scottlbaker/ADX-MINI/firmware/MI3/si5351.h

// ============================================================================
//
// si5351.h - Si5351 library for Arduino
//
// Copyright (C) 2015 - 2019 Jason Milldrum <milldrum@gmail.com>
//                           Dana H. Myers <k6jq@comcast.net>
//
// Some tuning algorithms derived from clk-si5351.c in the Linux kernel.
// Sebastian Hesselbarth <sebastian.hesselbarth@gmail.com>
// Rabeeh Khoury <rabeeh@solid-run.com>
//
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
// ============================================================================

#ifndef SI5351_H_
#define SI5351_H_

#define SI5351_I2C_ADDR                 0x60
#define SI5351_XTAL_FREQ                25000000
#define SI5351_PLL_FIXED                80000000000ULL
#define SI5351_FREQ_MULT                100ULL
#define SI5351_DEFAULT_CLK              1000000000ULL

#define SI5351_PLL_VCO_MIN              600000000
#define SI5351_PLL_VCO_MAX              900000000
#define SI5351_MULTISYNTH_MIN_FREQ      500000
#define SI5351_MULTISYNTH_DIVBY4_FREQ   150000000
#define SI5351_MULTISYNTH_MAX_FREQ      225000000
#define SI5351_MULTISYNTH_SHARE_MAX     100000000
#define SI5351_MULTISYNTH_SHARE_MIN     1024000
#define SI5351_CLKOUT_MIN_FREQ          4000
#define SI5351_CLKOUT_MAX_FREQ          SI5351_MULTISYNTH_MAX_FREQ

#define SI5351_PLL_A_MIN                15
#define SI5351_PLL_A_MAX                90
#define SI5351_PLL_B_MAX                (SI5351_PLL_C_MAX-1)
#define SI5351_PLL_C_MAX                1048575
#define SI5351_MULTISYNTH_A_MIN         6
#define SI5351_MULTISYNTH_A_MAX         1800
#define SI5351_MULTISYNTH_B_MAX         (SI5351_MULTISYNTH_C_MAX-1)
#define SI5351_MULTISYNTH_C_MAX         1048575
#define SI5351_MULTISYNTH_P1_MAX        ((1<<18)-1)
#define SI5351_MULTISYNTH_P2_MAX        ((1<<20)-1)
#define SI5351_MULTISYNTH_P3_MAX        ((1<<20)-1)
#define SI5351_VCXO_PULL_MIN            30
#define SI5351_VCXO_PULL_MAX            240
#define SI5351_VCXO_MARGIN              103

#define SI5351_DEVICE_STATUS            0
#define SI5351_INTERRUPT_STATUS         1
#define SI5351_INTERRUPT_MASK           2
#define SI5351_STATUS_SYS_INIT          (1<<7)
#define SI5351_STATUS_LOL_B             (1<<6)
#define SI5351_STATUS_LOL_A             (1<<5)
#define SI5351_STATUS_LOS               (1<<4)
#define SI5351_OUTPUT_ENABLE_CTRL       3
#define SI5351_OEB_PIN_ENABLE_CTRL      9
#define SI5351_PLL_INPUT_SOURCE         15
#define SI5351_PLL_INPUT_XO             0
#define SI5351_PLL_INPUT_CLKIN          1

#define SI5351_CLKIN_DIV_MASK           (3<<6)
#define SI5351_CLKIN_DIV_1              (0<<6)
#define SI5351_CLKIN_DIV_2              (1<<6)
#define SI5351_CLKIN_DIV_4              (2<<6)
#define SI5351_CLKIN_DIV_8              (3<<6)
#define SI5351_PLLB_SOURCE              (1<<3)
#define SI5351_PLLA_SOURCE              (1<<2)

#define SI5351_CLK0_CTRL                16
#define SI5351_CLK1_CTRL                17
#define SI5351_CLK2_CTRL                18
#define SI5351_CLK3_CTRL                19
#define SI5351_CLK4_CTRL                20
#define SI5351_CLK5_CTRL                21
#define SI5351_CLK6_CTRL                22
#define SI5351_CLK7_CTRL                23
#define SI5351_CLK_POWERDOWN            (1<<7)
#define SI5351_CLK_INTEGER_MODE         (1<<6)
#define SI5351_CLK_PLL_SELECT           (1<<5)
#define SI5351_CLK_INVERT               (1<<4)
#define SI5351_CLK_INPUT_MASK           (3<<2)
#define SI5351_CLK_INPUT_XTAL           (0<<2)
#define SI5351_CLK_INPUT_CLKIN          (1<<2)
#define SI5351_CLK_INPUT_MULTISYNTH_0_4 (2<<2)
#define SI5351_CLK_INPUT_MULTISYNTH_N   (3<<2)
#define SI5351_CLK_DRIVE_STRENGTH_MASK  (3<<0)
#define SI5351_CLK_DRIVE_STRENGTH_2MA   (0<<0)
#define SI5351_CLK_DRIVE_STRENGTH_4MA   (1<<0)
#define SI5351_CLK_DRIVE_STRENGTH_6MA   (2<<0)
#define SI5351_CLK_DRIVE_STRENGTH_8MA   (3<<0)

#define SI5351_CLK3_0_DISABLE_STATE     24
#define SI5351_CLK7_4_DISABLE_STATE     25
#define SI5351_CLK_DISABLE_STATE_MASK   3
#define SI5351_CLK_DISABLE_STATE_LOW    0
#define SI5351_CLK_DISABLE_STATE_HIGH   1
#define SI5351_CLK_DISABLE_STATE_FLOAT  2
#define SI5351_CLK_DISABLE_STATE_NEVER  3

#define SI5351_PARAMETERS_LENGTH        8
#define SI5351_PLLA_PARAMETERS          26
#define SI5351_PLLB_PARAMETERS          34
#define SI5351_CLK0_PARAMETERS          42
#define SI5351_CLK1_PARAMETERS          50
#define SI5351_CLK2_PARAMETERS          58
#define SI5351_CLK3_PARAMETERS          66
#define SI5351_CLK4_PARAMETERS          74
#define SI5351_CLK5_PARAMETERS          82
#define SI5351_CLK6_PARAMETERS          90
#define SI5351_CLK7_PARAMETERS          91
#define SI5351_CLK6_7_OUTPUT_DIVIDER    92
#define SI5351_OUTPUT_CLK_DIV_MASK      (7 << 4)
#define SI5351_OUTPUT_CLK6_DIV_MASK     (7 << 0)
#define SI5351_OUTPUT_CLK_DIV_SHIFT     4
#define SI5351_OUTPUT_CLK_DIV6_SHIFT    0
#define SI5351_OUTPUT_CLK_DIV_1         0
#define SI5351_OUTPUT_CLK_DIV_2         1
#define SI5351_OUTPUT_CLK_DIV_4         2
#define SI5351_OUTPUT_CLK_DIV_8         3
#define SI5351_OUTPUT_CLK_DIV_16        4
#define SI5351_OUTPUT_CLK_DIV_32        5
#define SI5351_OUTPUT_CLK_DIV_64        6
#define SI5351_OUTPUT_CLK_DIV_128       7
#define SI5351_OUTPUT_CLK_DIVBY4       (3<<2)

#define SI5351_CLK0                     0
#define SI5351_CLK1                     1
#define SI5351_CLK2                     2
#define SI5351_CLK3                     3
#define SI5351_CLK4                     4
#define SI5351_CLK5                     5
#define SI5351_CLK6                     6
#define SI5351_CLK7                     7

#define SI5351_SSC_PARAM0               149
#define SI5351_SSC_PARAM1               150
#define SI5351_SSC_PARAM2               151
#define SI5351_SSC_PARAM3               152
#define SI5351_SSC_PARAM4               153
#define SI5351_SSC_PARAM5               154
#define SI5351_SSC_PARAM6               155
#define SI5351_SSC_PARAM7               156
#define SI5351_SSC_PARAM8               157
#define SI5351_SSC_PARAM9               158
#define SI5351_SSC_PARAM10              159
#define SI5351_SSC_PARAM11              160
#define SI5351_SSC_PARAM12              161

#define SI5351_VXCO_PARAMETERS_LOW      162
#define SI5351_VXCO_PARAMETERS_MID      163
#define SI5351_VXCO_PARAMETERS_HIGH     164

#define SI5351_CLK0_PHASE_OFFSET        165
#define SI5351_CLK1_PHASE_OFFSET        166
#define SI5351_CLK2_PHASE_OFFSET        167
#define SI5351_CLK3_PHASE_OFFSET        168
#define SI5351_CLK4_PHASE_OFFSET        169
#define SI5351_CLK5_PHASE_OFFSET        170

#define SI5351_PLLA                     0
#define SI5351_PLLB                     1
#define SI5351_PLL_RESET                177
#define SI5351_PLL_RESET_B              (1<<7)
#define SI5351_PLL_RESET_A              (1<<5)
#define SI5351_CRYSTAL_LOAD             183
#define SI5351_CRYSTAL_LOAD_MASK        (3<<6)
#define SI5351_CRYSTAL_LOAD_0PF         (0<<6)
#define SI5351_CRYSTAL_LOAD_6PF         (1<<6)
#define SI5351_CRYSTAL_LOAD_8PF         (2<<6)
#define SI5351_CRYSTAL_LOAD_10PF        (3<<6)

#define SI5351_FANOUT_ENABLE            187
#define SI5351_CLKIN_ENABLE             (1<<7)
#define SI5351_XTAL_ENABLE              (1<<6)
#define SI5351_MULTISYNTH_ENABLE        (1<<4)

#define SI5351_DRIVE_2MA                0x00
#define SI5351_DRIVE_4MA                0x01
#define SI5351_DRIVE_6MA                0x02
#define SI5351_DRIVE_8MA                0x03

/* Macro definitions */

//#define RFRAC_DENOM ((1L << 20) - 1)
#define RFRAC_DENOM 1000000ULL

/*
 * The semantics of do_div() are:
 *
 * uint32_t do_div(uint64_t *n, uint32_t base)
 * {
 *      uint32_t remainder = *n % base;
 *      *n = *n / base;
 *      return remainder;
 * }
 *
 * NOTE: macro parameter n is evaluated multiple times,
 *       beware of side effects!
 */

# define do_div(n,base) ({                                      \
        uint64_t __base = (base);                               \
        uint64_t __rem;                                         \
        __rem = ((uint64_t)(n)) % __base;                       \
        (n) = ((uint64_t)(n)) / __base;                         \
        __rem;                                                  \
 })

/* Struct definitions */

struct Si5351RegSet {
  uint32_t p1;
  uint32_t p2;
  uint32_t p3;
};

class Si5351 {

public:
  // functions
  void init(void);
  void set_freq(uint64_t, uint8_t);
  void set_pll(uint64_t, uint8_t);
  void set_ms(uint8_t, struct Si5351RegSet, uint8_t, uint8_t, uint8_t);
  void output_enable(uint8_t, uint8_t);
  void drive_strength(uint8_t, uint8_t);
  void set_correction(int32_t, uint8_t);
  void pll_reset(uint8_t);
  void set_ms_source(uint8_t, uint8_t);
  void set_int(uint8_t, uint8_t);
  void set_clock_pwr(uint8_t, uint8_t);
  void write_bulk(uint8_t, uint8_t, uint8_t *);
  void write_reg(uint8_t, uint8_t);
  uint8_t read_reg(uint8_t);
  void powerDown(void);
  // variables
  uint8_t  pll_assignment[3];
  uint64_t plla_freq;
  uint64_t pllb_freq;
  uint8_t  plla_ref_osc;
  uint8_t  pllb_ref_osc;
  uint32_t xtal_freq[2];

private:
  // functions
  uint64_t pll_calc(uint8_t, uint64_t, struct Si5351RegSet*, int32_t, uint8_t);
  uint64_t multisynth_calc(uint64_t, uint64_t, struct Si5351RegSet*);
  void     ms_div(uint8_t, uint8_t, uint8_t);
  uint8_t  select_r_div(uint64_t *);
  // variables
  int32_t ref_correction[2];
  uint8_t clkin_div;
};

#endif
